Bspease/Senior-Project/Hardware/Next_Iteration/5.6Inductor.SLDPRT

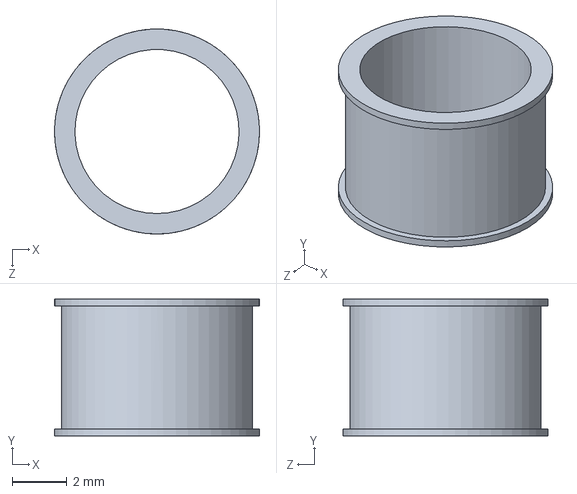
[picture p28: CAD file, 2021-12-21]
Hardware/Next_Iteration/5.6Inductor.SLDPRT
7.50 x 5.00 x 7.50 mm
