Bspease/Senior-Project/Hardware/Next_Iteration/Next_Iteration/Runner.SLDPRT

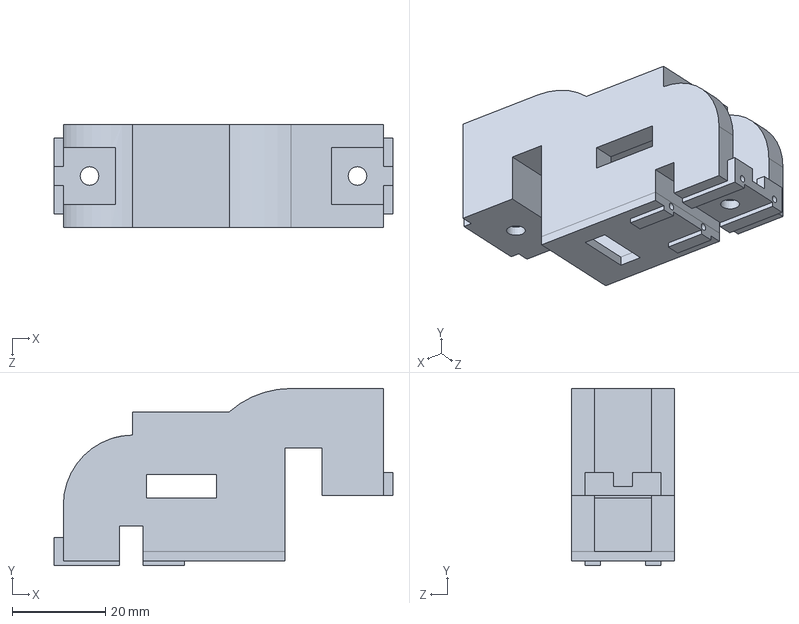
[picture p29: CAD file, 2021-12-21]
Hardware/Next_Iteration/Next_Iteration/Runner.SLDPRT
72.8 x 38.0 x 22.0 mm
