Bspease/Senior-Project/Hardware/TestServo.SLDPRT

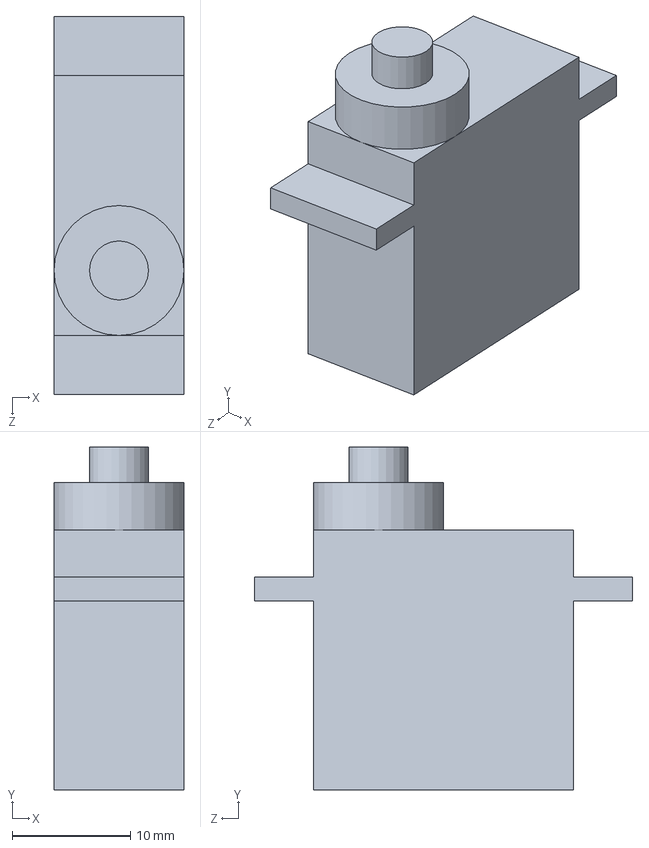
[picture p30: CAD file, 2021-12-21]
Hardware/TestServo.SLDPRT
11.0 x 29.0 x 32.0 mm
