Bspease/Senior-Project/Hardware/Next_Iteration/Next_Iteration/Body1.SLDPRT

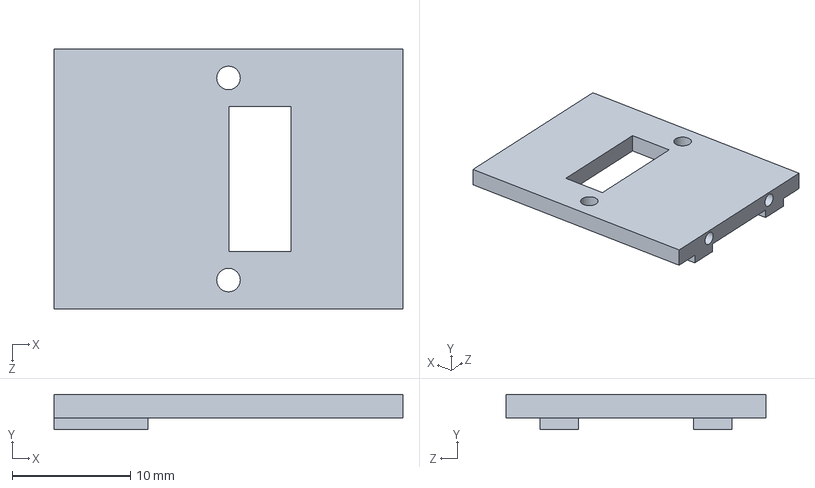
[picture p31: CAD file, 2021-12-21]
Hardware/Next_Iteration/Next_Iteration/Body1.SLDPRT
29.6 x 3.00 x 22.0 mm
