Bspease/Senior-Project/Hardware/Next_Iteration/RunnerAlt.SLDPRT

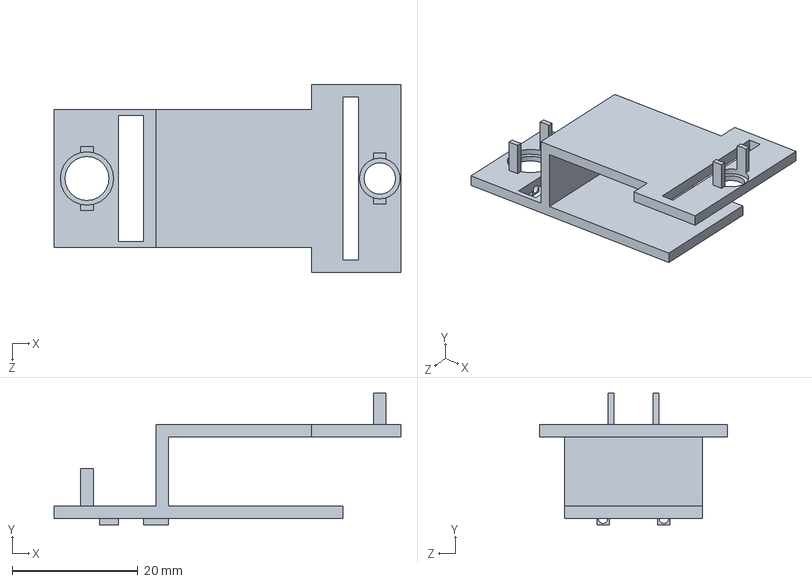
[picture p32: CAD file, 2021-12-21]
Hardware/Next_Iteration/RunnerAlt.SLDPRT
55.2 x 21.0 x 30.0 mm
