Bspease/Senior-Project/Hardware/BaseBasic.SLDPRT

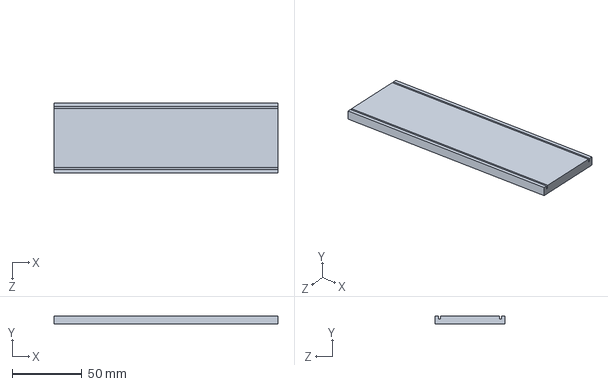
[picture p33: CAD file, 2021-12-21]
Hardware/BaseBasic.SLDPRT
160.0 x 6.00 x 50.0 mm
