Bspease/Senior-Project/Hardware/Next_Iteration/Next_Iteration/Next_Iteration/Runner2.SLDPRT

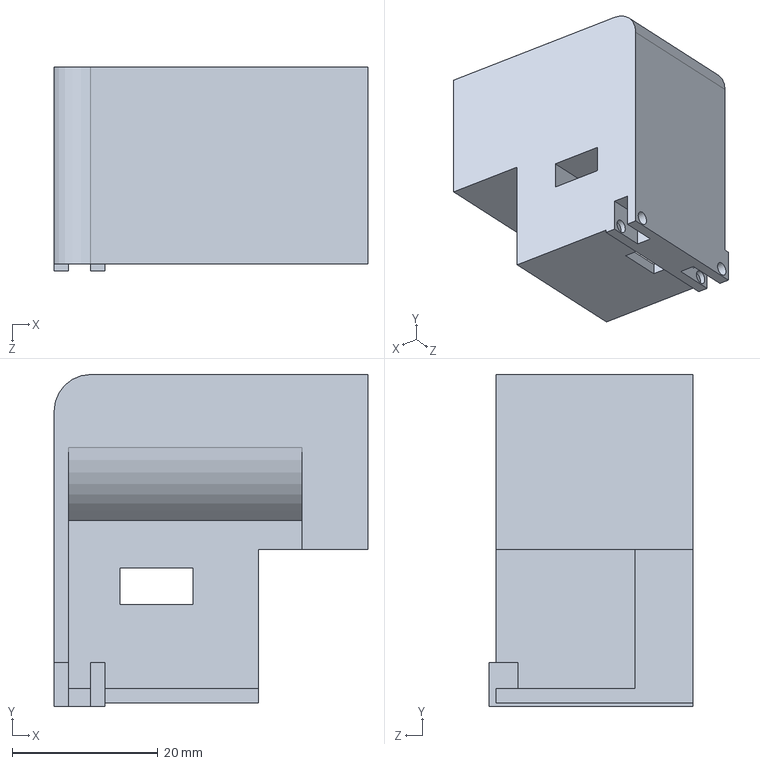
[picture p34: CAD file, 2021-12-21]
Hardware/Next_Iteration/Next_Iteration/Next_Iteration/Runner2.SLDPRT
43.0 x 45.5 x 28.0 mm
