Bspease/Senior-Project/Hardware/Next_Iteration/Next_Iteration/SmallWheel.SLDPRT

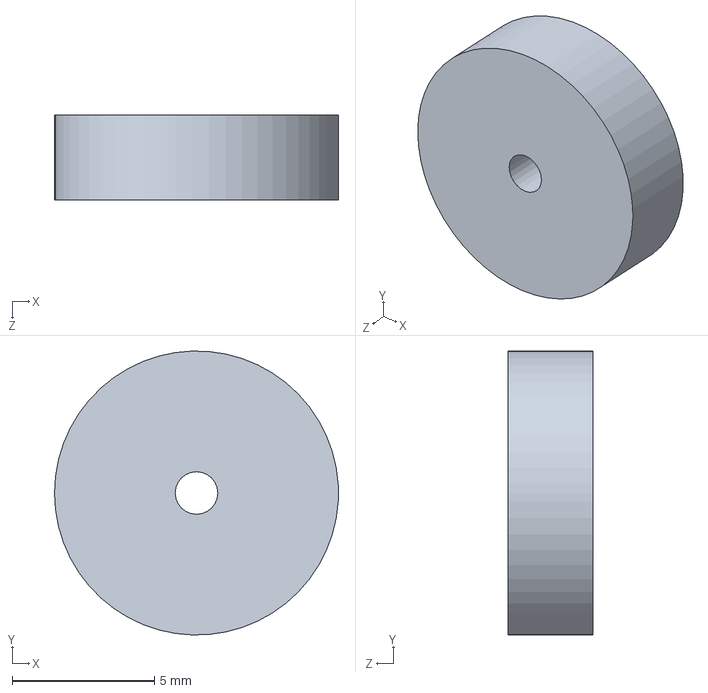
[picture p35: CAD file, 2021-12-21]
Hardware/Next_Iteration/Next_Iteration/SmallWheel.SLDPRT
10.0 x 10.00 x 3.00 mm
