Bspease/Senior-Project/Hardware/Next_Iteration/SmallWheel.SLDPRT

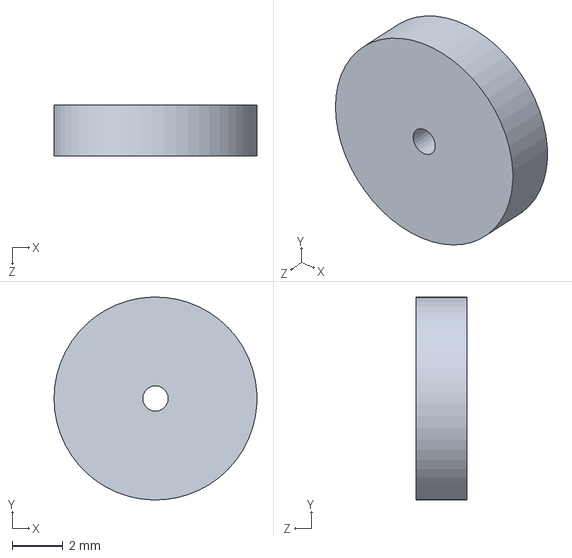
[picture p36: CAD file, 2021-12-21]
Hardware/Next_Iteration/SmallWheel.SLDPRT
8.00 x 8.00 x 2.00 mm
