Bspease/Senior-Project/Hardware/RunnerLever.SLDPRT

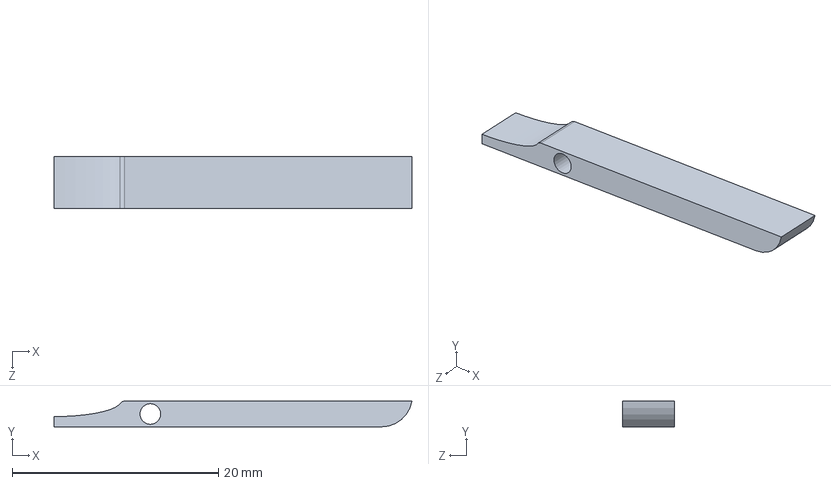
[picture p37: CAD file, 2021-12-21]
Hardware/RunnerLever.SLDPRT
34.8 x 2.50 x 5.00 mm
