Bspease/Senior-Project/Hardware/Next_Iteration/4.13LPress.SLDPRT

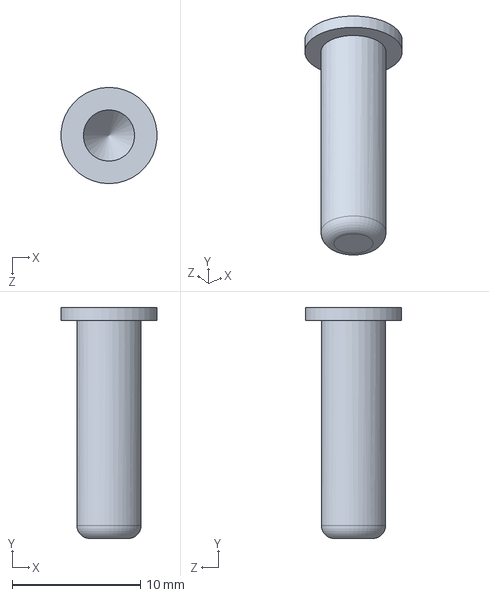
[picture p38: CAD file, 2021-12-21]
Hardware/Next_Iteration/4.13LPress.SLDPRT
7.47 x 18.0 x 7.50 mm
