Bspease/Senior-Project/Hardware/Next_Iteration/5.14LPress.SLDPRT

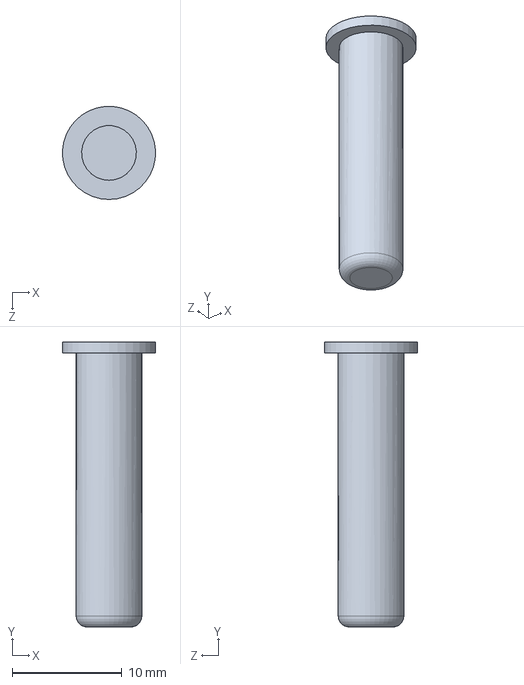
[picture p39: CAD file, 2021-12-21]
Hardware/Next_Iteration/5.14LPress.SLDPRT
8.49 x 26.0 x 8.48 mm
