Bspease/Senior-Project/Hardware/RunnerAxel.SLDPRT

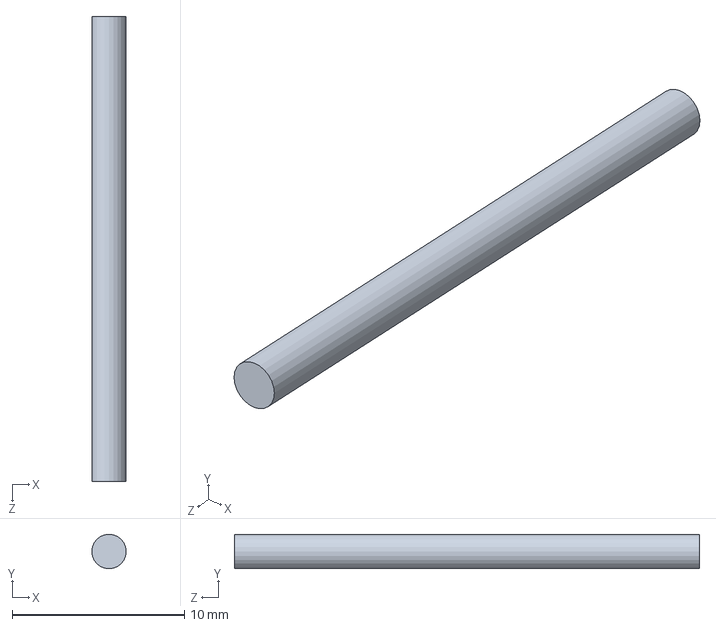
[picture p40: CAD file, 2021-12-21]
Hardware/RunnerAxel.SLDPRT
2.00 x 2.00 x 27.0 mm
