Bspease/Senior-Project/Hardware/Part1.SLDPRT

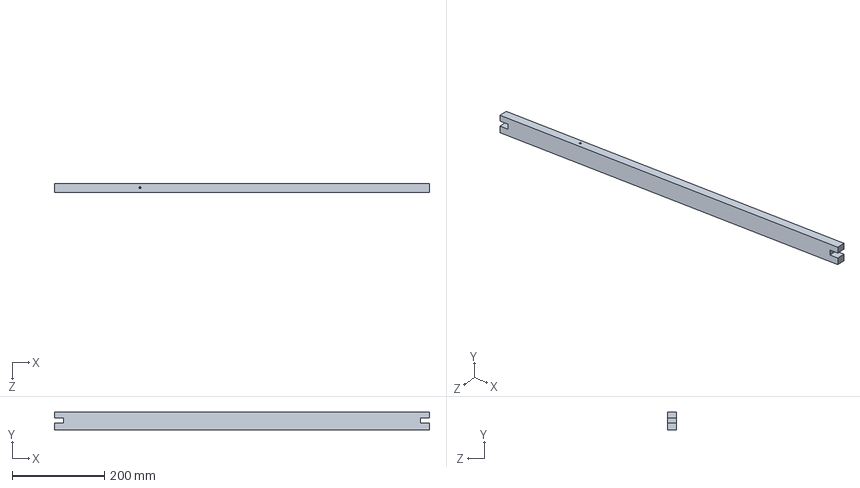
[picture p41: CAD file, 2021-12-21]
Hardware/Part1.SLDPRT
812.8 x 38.1 x 19.1 mm
